pushtiujeniya/esp32-c6-environmental-logger/3d view/3D_Bottom view.jpg

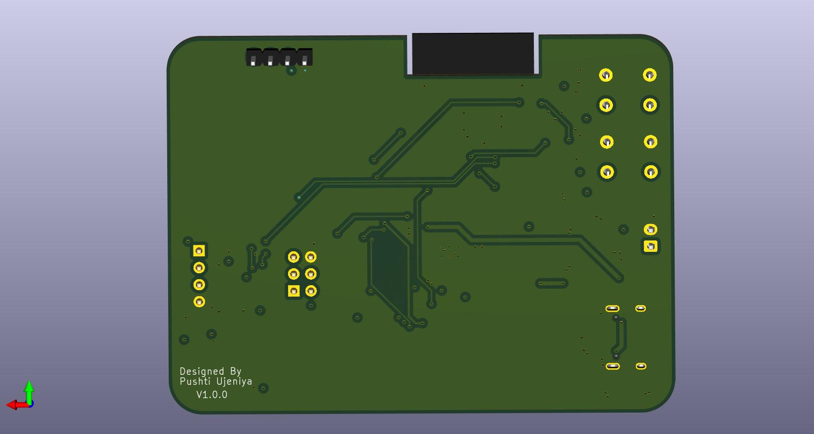
3d view/3D_Bottom view.jpg
