pushtiujeniya/esp32-c6-environmental-logger/layout images/Screenshot 2026-06-21 155747.png

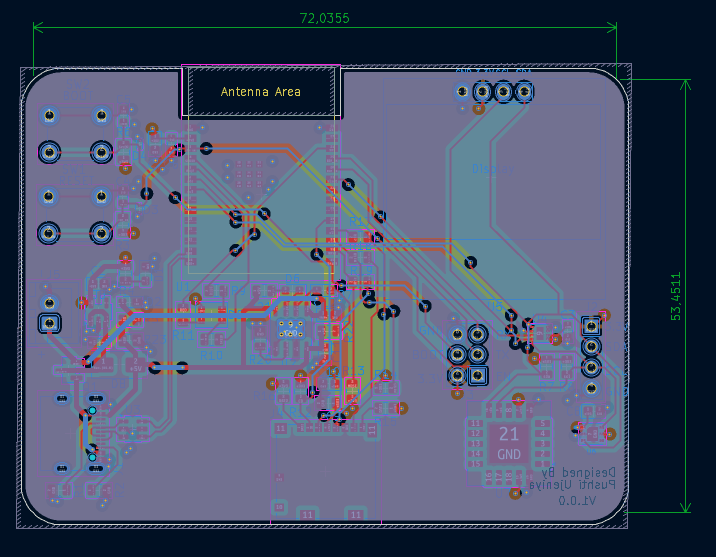
layout images/Screenshot 2026-06-21 155747.png
